DLehenbauer/commodore-pet-clone/rtl/t8/PET/src/main.sv

/**
 * PET Clone - Open hardware implementation of the Commodore PET
 * by Daniel Lehenbauer and contributors.
 * 
 * https://github.com/DLehenbauer/commodore-pet-clone
 *
 * To the extent possible under law, I, Daniel Lehenbauer, have waived all
 * copyright and related or neighboring rights to this project. This work is
 * published from the United States.
 *
 * @copyright CC0 http://creativecommons.org/publicdomain/zero/1.0/
 * @author Daniel Lehenbauer <DLehenbauer@users.noreply.github.com> and contributors
 */

module main(
    // FPGA
    input  logic clk16_i,

    // SPI1
    input  logic spi1_sck_i,
    input  logic spi1_cs_ni,
    input  logic spi1_rx_i,
    output logic spi1_tx_o,
    output logic spi_ready_o,

    // System Bus
    input  logic [15:0]  bus_addr_i,
    output logic [16:0]  bus_addr_o,
    output logic         bus_addr_oe,

    input  logic  [7:0]  bus_data_i,
    output logic  [7:0]  bus_data_o,
    output logic         bus_data_oe,

    input  logic         bus_rw_ni,
    output logic         bus_rw_no,
    output logic         bus_rw_noe,
   
    // CPU
    output logic cpu_clk_o,
    output logic cpu_res_o,
    input  logic cpu_res_i,
    output logic cpu_ready_o,
    output logic cpu_be_o,

    // RAM
    output logic ram_oe_o,
    output logic ram_we_o,
    output logic [11:10] ram_addr_o,

    // I/O
    output logic pia1_cs_o,
    output logic pia2_cs_o,
    output logic via_cs_o,
    output logic io_oe_o,

    // Audio
    input  logic diag_i,
    input  logic via_cb2_i,
    output logic audio_o,

    // Graphics
    input  logic gfx_i,
    output logic h_sync_o,
    output logic v_sync_o,
    output logic video_o
);
    //
    // SPI1
    //

    logic        spi_rw_n;      // Direction (0 = Write, 1 = Read)
    logic [16:0] spi_addr;      // 17-bit address of pending transaction
    logic  [7:0] spi_wr_data;   // Data from MCU when writing
    logic  [7:0] spi_rd_data;   // Data to MCU when reading
    logic        spi_valid;     // Transaction pending: spi_addr, _data, and _rw_n are valid
    logic        spi_ready;     // Transaction complete: ready for next SPI command
    
    spi1 spi1(
        .clk_sys_i(clk16_i),
        .spi_sck_i(spi1_sck_i),
        .spi_cs_ni(spi1_cs_ni),
        .spi_rx_i(spi1_rx_i),
        .spi_tx_o(spi1_tx_o),
        .spi_valid_o(spi_valid),
        .spi_ready_i(spi_ready),
        .spi_ready_o(spi_ready_o),
        .spi_addr_o(spi_addr),
        .spi_data_i(spi_rd_data),
        .spi_data_o(spi_wr_data),
        .spi_rw_no(spi_rw_n)
    );

    //
    // Timing
    //

    logic strobe_clk;
    logic setup_clk;
    logic cpu_en;
    logic spi_en;
    logic vram0_en;
    logic vrom0_en;
    logic vram1_en;
    logic vrom1_en;

    timing timing(
        .clk16_i(clk16_i),
        .strobe_clk_o(strobe_clk),
        .setup_clk_o(setup_clk),

        .spi_en_o(spi_en),
        .spi_valid_i(spi_valid),
        .spi_ready_o(spi_ready),
        
        .cpu_be_o(cpu_be_o),
        .cpu_en_o(cpu_en),
        .cpu_clk_o(cpu_clk_o),

        .vram0_en_o(vram0_en),
        .vrom0_en_o(vrom0_en),
        .vram1_en_o(vram1_en),
        .vrom1_en_o(vrom1_en)
    );
    
    wire cpu_rd_en = cpu_en &&  bus_rw_ni;          // Enable for CPU write
    wire cpu_wr_en = cpu_en && !bus_rw_ni;          // Enable for CPU read

    wire spi_rd_en = spi_en &&  spi_rw_n;           // Enable for SPI read transaction
    wire spi_wr_en = spi_en && !spi_rw_n;           // Enable for SPI write transaction

    //
    // Address Decoding
    //

    logic ram_en;
    logic pia1_en;
    logic pia2_en;
    logic via_en;
    logic crtc_en;
    logic sid_en;
    logic io_en;
    logic is_mirrored;

    address_decoding address_decoding(
        .addr_i({ bus_addr_o[16], bus_addr_i}),
        .ram_en_o(ram_en),
        .pia1_en_o(pia1_en),
        .pia2_en_o(pia2_en),
        .via_en_o(via_en),
        .crtc_en_o(crtc_en),
        .sid_en_o(sid_en),
        .io_en_o(io_en),
        .is_mirrored_o(is_mirrored)
    );
    
    logic [7:0] kbd_data;
    logic       kbd_data_oe;

    keyboard keyboard(
        .strobe_clk_i(strobe_clk),
        .spi_addr_i(spi_addr),
        .spi_data_i(spi_wr_data),
        .spi_wr_en_i(spi_wr_en),
        .pia1_rs_i(bus_addr_i[1:0]),
        .bus_data_i(bus_data_i),
        .pia1_en_i(pia1_en),
        .cpu_rd_en_i(cpu_rd_en),
        .cpu_wr_en_i(cpu_wr_en),
        .kbd_data_o(kbd_data),
        .kbd_data_oe(kbd_data_oe)
    );

    assign pia1_cs_o = !kbd_data_oe && pia1_en && cpu_en;
    assign pia2_cs_o = pia2_en && cpu_en;
    assign via_cs_o  =  via_en && cpu_en;
    assign io_oe_o   = !kbd_data_oe && io_en && cpu_en;

    control control(
        .strobe_clk_i(strobe_clk),
        .spi_addr_i(spi_addr),
        .spi_data_i(spi_wr_data),
        .spi_wr_en_i(spi_wr_en),
        .cpu_res_o(cpu_res_o),
        .cpu_ready_o(cpu_ready_o)
    );

    //
    // Audio
    //

    audio audio(
        .reset_i(cpu_res_i),
        .clk8_i(strobe_clk),
        .cpu_en_i(cpu_en),
        .cpu_wr_en_i(cpu_wr_en),
        .sid_en_i(sid_en),
        .addr_i(bus_addr_i[4:0]),
        .data_i(bus_data_i),
        .diag_i(diag_i),
        .via_cb2_i(via_cb2_i),
        .audio_o(audio_o)
    );

    //
    // Video
    //

    logic [13:0] video_addr;
    logic        video_addr_oe;

    video video(
        .reset_i(cpu_res_i),
        .clk16_i(clk16_i),
        .pixel_clk_i(setup_clk),
        .setup_clk_i(setup_clk),
        .strobe_clk_i(strobe_clk),
        .cpu_en_i(cpu_en),
        .cclk_en_i(cpu_en),
        .vram0_en_i(vram0_en),
        .vrom0_en_i(vrom0_en),
        .vram1_en_i(vram1_en),
        .vrom1_en_i(vrom1_en),
        .crtc_en_i(crtc_en),
        .rw_ni(bus_rw_ni),
        .addr_i(bus_addr_i[0]),
        .addr_o(video_addr),
        .addr_oe(video_addr_oe),
        .data_i(bus_data_i),
        .gfx_i(gfx_i),
        .h_sync_o(h_sync_o),
        .v_sync_o(v_sync_o),
        .video_o(video_o)
    );

    assign ram_addr_o[11:10] = is_mirrored && cpu_en
        ? 2'b00 // 80 col: { 1'b0, bus_addr_i[10:10] }
        : bus_addr_i[11:10];

    //
    // RAM
    //

    assign ram_oe_o = ram_en && (spi_rd_en || cpu_rd_en || vram0_en || vrom0_en || vram1_en || vrom1_en);   // RAM output enable
    assign ram_we_o = ram_en && (spi_wr_en || cpu_wr_en) && strobe_clk;                                     // RAM write strobe
    
    //
    // Bus
    //

    assign bus_rw_noe   = spi_en;
    assign bus_rw_no    = spi_rw_n;

    assign bus_addr_oe  = spi_en || video_addr_oe;
    assign bus_addr_o   = spi_en
        ? spi_addr
        : { 3'b010, video_addr };

    assign bus_data_oe  = spi_wr_en || kbd_data_oe;
    assign bus_data_o   = kbd_data_oe
        ? kbd_data
        : spi_wr_data;

    always @(negedge strobe_clk) begin
        if (spi_rd_en) begin
            if (spi_addr == 17'h0e80f) spi_rd_data <= { 7'h0, gfx_i };
            else spi_rd_data <= bus_data_i;
        end
    end
endmodule
