DLehenbauer/commodore-pet-clone/rtl/ep2/bus.sv

/**
 * PET Clone - Open hardware implementation of the Commodore PET
 * by Daniel Lehenbauer and contributors.
 * 
 * https://github.com/DLehenbauer/commodore-pet-clone
 *
 * To the extent possible under law, I, Daniel Lehenbauer, have waived all
 * copyright and related or neighboring rights to this project. This work is
 * published from the United States.
 *
 * @copyright CC0 http://creativecommons.org/publicdomain/zero/1.0/
 * @author Daniel Lehenbauer <DLehenbauer@users.noreply.github.com> and contributors
 */

module bus(
    input  clk16,
    output clk8,
    output pi_select,
    output pi_strobe,
    output video_select,
    output video_ram_strobe,
    output video_rom_strobe,
    output cpu_select,
    output io_select,
    output cpu_strobe
);
    // ncount          0   1   2   3   4   5   6   7   8   9  10  11  12  13  14  15   0
    // pcount        0   1   2   3   4   5   6   7   8   9  10  11  12  13  14  15   0
    // edge          1 . 3 . 5 . 7 . 9 .11 .13 .15 .17 .19 .21 .23 .25 .27 .29 .31 . 1 .
    //               : . : . : . : . : . : . : . : . : . : . : . : . : . : . : . : . : . 
    //     clk_16   _/‾\_/‾\_/‾\_/‾\_/‾\_/‾\_/‾\_/‾\_/‾\_/‾\_/‾\_/‾\_/‾\_/‾\_/‾\_/‾\_/‾\_
    //               : . : . : . : . : . : . : . : . : . : . : . : . : . : . : . : . : . 
    //      clk_8   ‾\___/‾‾‾\___/‾‾‾\___/‾‾‾\___/‾‾‾\___/‾‾‾\___/‾‾‾\___/‾‾‾\___/‾‾‾\___
    //               : . : . : . : . : . : . : . : . : . : . : . : . : . : . : . : . : . 
    //  pi_select   _/‾‾‾‾‾‾‾\_______________________________________________________/‾‾‾
    //               : . : . : . : . : . : . : . : . : . : . : . : . : . : . : . : . : . 
    //  pi_strobe   _____/‾‾‾\___________________________________________________________
    //               : . : . : . : . : . : . : . : . : . : . : . : . : . : . : . : . : . 
    //  video_sel   _____________/‾‾‾‾‾‾‾‾‾‾‾‾‾‾‾‾‾‾‾‾‾‾‾‾‾‾‾‾‾‾‾‾‾‾‾\___________________
    //               : . : . : . : . : . : . : . : . : . : . : . : . : . : . : . : . : . 
    //  video_ram   _________________/‾‾‾\_______________________________________________
    //               : . : . : . : . : . : . : . : . : . : . : . : . : . : . : . : . : . 
    //  video_rom   _________________________/‾‾‾\_______________________________________
    //               : . : . : . : . : . : . : . : . : . : . : . : . : . : . : . : . : . 
    // cpu_select   _________________________________________________/‾‾‾‾‾‾‾‾‾‾‾‾‾‾‾\___
    //               : . : . : . : . : . : . : . : . : . : . : . : . : . : . : . : . : . 
    //  io_select   _____________________________________________________/‾‾‾‾‾‾‾‾‾‾‾\___
    //               : . : . : . : . : . : . : . : . : . : . : . : . : . : . : . : . : . 
    // cpu_strobe   _________________________________________________________/‾‾‾\_______
    //
    // Note: edge # = count * 2 + 1
    //       { rise edge #, fall edge #, rise edge # + 32 }

    localparam [7:0] PI_SELECT          = 8'b00000001,
                     PI_STROBE          = 8'b00000011,
                     VIDEO_SELECT       = 8'b00000100,
                     VIDEO_RAM_STROBE   = 8'b00001100,
                     VIDEO_ROM_STROBE   = 8'b00010100,
                     CPU_SELECT         = 8'b00100000,
                     IO_SELECT          = 8'b01100000,
                     CPU_STROBE         = 8'b11100000;

    reg [3:0] count = 0;
    reg [7:0] state = PI_SELECT, next = PI_SELECT;
    
    always @(posedge clk16) begin
        count <= count + 4'h1;
        state <= next;
    end
    
    always @(count) begin
        next = 8'bxxxxxxxx;
        case (count)
            0:  next = PI_SELECT;
            1:  next = PI_STROBE;
            2:  next = PI_SELECT;
            3:  next = VIDEO_SELECT;
            4:  next = VIDEO_RAM_STROBE;
            5:  next = VIDEO_SELECT;
            6:  next = VIDEO_ROM_STROBE;
            7:  next = VIDEO_SELECT;
            8:  next = VIDEO_SELECT;
            9:  next = VIDEO_SELECT;
            10: next = VIDEO_SELECT;
            11: next = VIDEO_SELECT;
            12: next = CPU_SELECT;
            13: next = IO_SELECT;
            14: next = CPU_STROBE;
            15: next = IO_SELECT;
        endcase
    end

    assign pi_select        = state[0];
    assign pi_strobe        = state[1];
    assign video_select     = state[2];
    assign video_ram_strobe = state[3];
    assign video_rom_strobe = state[4];
    assign cpu_select       = state[5];
    assign io_select        = state[6];
    assign cpu_strobe       = state[7];

    assign clk8 = count[0];
endmodule
