DLehenbauer/commodore-pet-clone/rtl/t8/PET/src/video_dotgen.sv

/**
 * PET Clone - Open hardware implementation of the Commodore PET
 * by Daniel Lehenbauer and contributors.
 * 
 * https://github.com/DLehenbauer/commodore-pet-clone
 *
 * To the extent possible under law, I, Daniel Lehenbauer, have waived all
 * copyright and related or neighboring rights to this project. This work is
 * published from the United States.
 *
 * @copyright CC0 http://creativecommons.org/publicdomain/zero/1.0/
 * @author Daniel Lehenbauer <DLehenbauer@users.noreply.github.com> and contributors
 */

module dotgen(
    input  logic        clk_i,
    input  logic        pixel_clk_en,
    input  logic        video_latch,
    input  logic [15:0] pixels_i,
    input  logic [1:0]  reverse_i,
    input  logic        display_en_i,
    output logic        video_o
);
    logic [3:0]  pixel_ctr_d, pixel_ctr_q;
    logic [15:0] sr_out_d, sr_out_q;
    logic [1:0]  reverse_d, reverse_q;
    logic        display_en_d, display_en_q;

    always_comb begin
        if (video_latch) begin
            pixel_ctr_d = '0;
            sr_out_d = pixels_i;
            reverse_d = reverse_i;
            display_en_d = display_en_i;
        end else begin
            pixel_ctr_d = pixel_ctr_q + 1'b1;
            sr_out_d = { sr_out_q[14:0], 1'b0 };
            reverse_d = reverse_q;
            display_en_d = display_en_q;
        end
    end

    always_ff @(posedge clk_i) begin
        if (pixel_clk_en) begin
            pixel_ctr_q  <= pixel_ctr_d;
            sr_out_q     <= sr_out_d;
            reverse_q    <= reverse_d;
            display_en_q <= display_en_d;
        end
    end

    assign video_o = display_en_q & (sr_out_q[15] ^ reverse_q[~pixel_ctr_q[3]]);
endmodule
