DLehenbauer/commodore-pet-clone/rtl/t8/PET/src/keyboard.sv

/**
 * PET Clone - Open hardware implementation of the Commodore PET
 * by Daniel Lehenbauer and contributors.
 * 
 * https://github.com/DLehenbauer/commodore-pet-clone
 *
 * To the extent possible under law, I, Daniel Lehenbauer, have waived all
 * copyright and related or neighboring rights to this project. This work is
 * published from the United States.
 *
 * @copyright CC0 http://creativecommons.org/publicdomain/zero/1.0/
 * @author Daniel Lehenbauer <DLehenbauer@users.noreply.github.com> and contributors
 */
 
 module keyboard(
    input  logic strobe_clk_i,
 
    input  logic [16:0] spi_addr_i,         // 17-bit address from pending SPI transaction
    input  logic  [7:0] spi_data_i,         // Data from pending SPI transaction
    input  logic        spi_wr_en_i,        // Asserted when SPI is writing

    input  logic        pia1_en_i,          // PIA1 chip select (from address decoding)
    input  logic  [1:0] pia1_rs_i,          // PIA1 register select (from bus_addr[1:0])
    
    input  logic  [7:0] bus_data_i,         // Data from pending bus transaction
    input  logic        cpu_rd_en_i,
    input  logic        cpu_wr_en_i,

    output logic  [7:0] kbd_data_o,
    output logic        kbd_data_oe
);
    localparam PORTA = 2'd0,
               CRA   = 2'd1,
               PORTB = 2'd2,
               CRB   = 2'd3;

    logic [7:0] kbd_matrix [16];
    logic [3:0] current_kbd_row = '0;
    
    logic spi_wr_matrix;

    always_comb begin
        casez (spi_addr_i)
            17'hE80?: spi_wr_matrix = spi_wr_en_i;
            default:  spi_wr_matrix = '0;
        endcase
    end

    // Save the selected keyboard row when the CPU writes to port A ($E810)
    wire writing_port_a = cpu_wr_en_i && pia1_en_i && pia1_rs_i == PORTA;

    always @(negedge strobe_clk_i) begin
        if (spi_wr_matrix) kbd_matrix[spi_addr_i[3:0]] <= spi_data_i;
        else if (writing_port_a) current_kbd_row <= bus_data_i[3:0];
        else kbd_data_o <= kbd_matrix[current_kbd_row];
    end

    wire reading_port_b = cpu_rd_en_i && pia1_en_i && pia1_rs_i == PORTB;

    // Intercept reads to port B ($E812) only when the cached key matrix has a pressed key.
    // Otherwise, reads should go to PIA1 so that the standard PET keyboard also works.
    assign kbd_data_oe = reading_port_b && kbd_data_o != 8'hff;
endmodule
